diponk24/project-jafar-prosthetic-arm/JAFAR CAD pre-modified/ARM/DIFFERENTIAL/TOP.stl

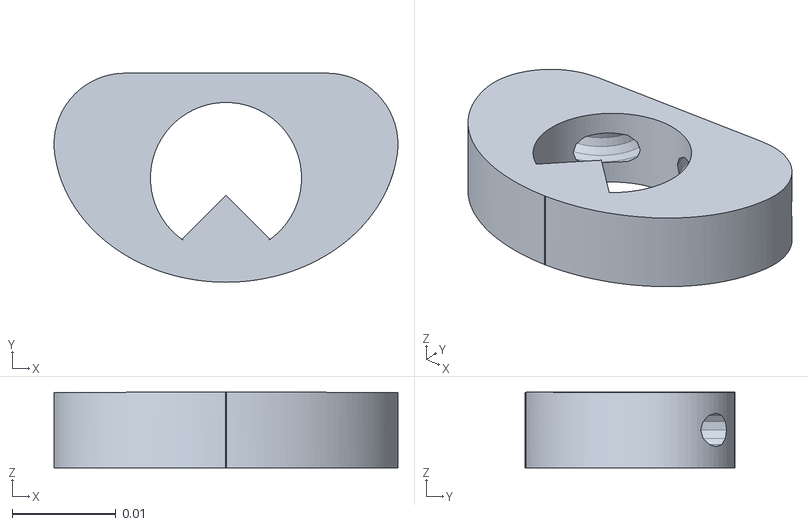
[picture p24: CAD file, 2026-06-13]
JAFAR CAD pre-modified/ARM/DIFFERENTIAL/TOP.stl
0.0332 x 0.0202 x 0.00731
