diponk24/project-jafar-prosthetic-arm/JAFAR CAD post modification/Fingers/Arm/base.stl

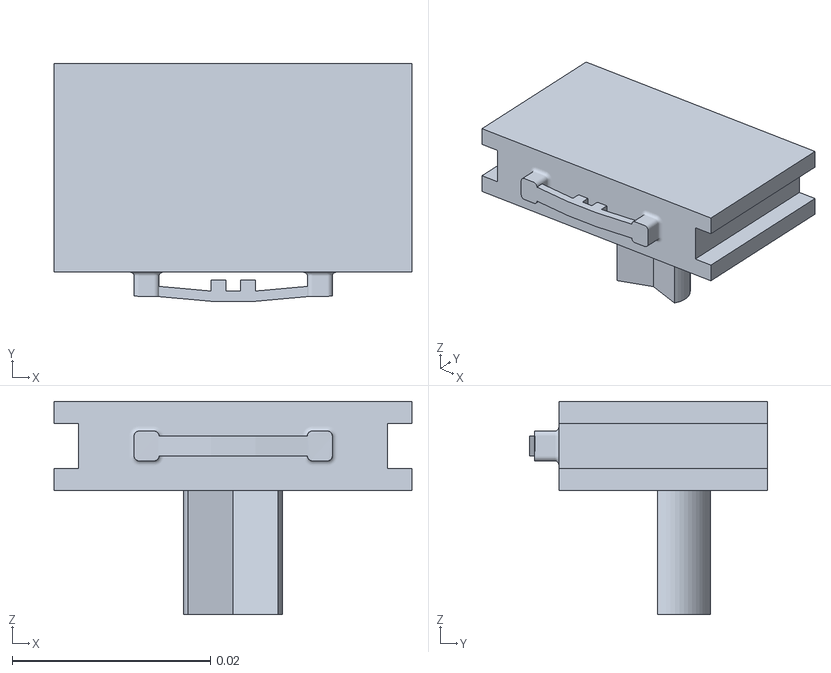
[picture p25: CAD file, 2026-06-13]
JAFAR CAD post modification/Fingers/Arm/base.stl
0.0361 x 0.0239 x 0.0215
