diponk24/project-jafar-prosthetic-arm/JAFAR CAD post modification/Fingers/little_m.stl

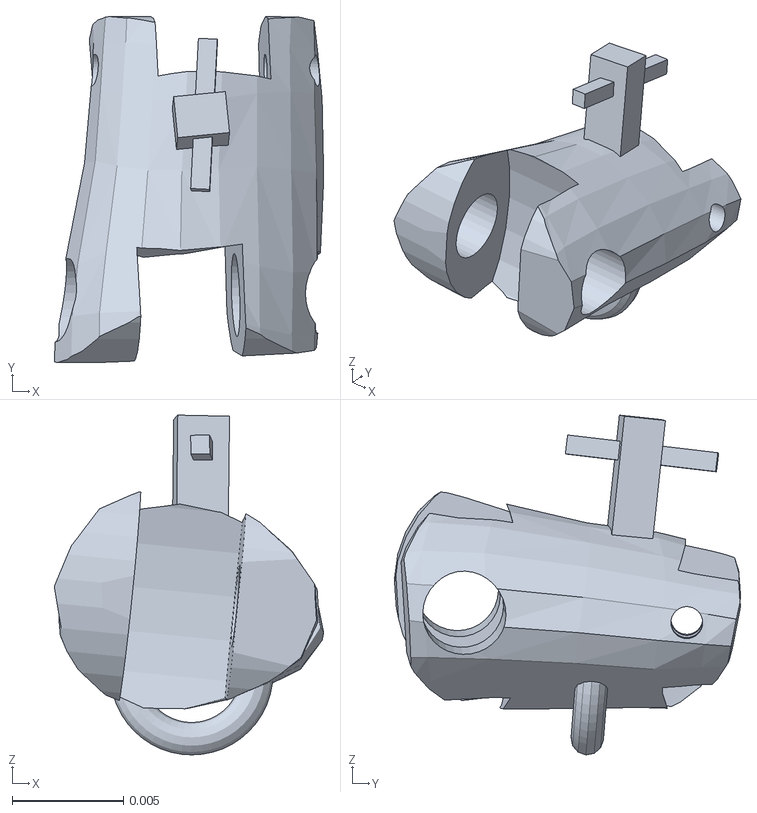
[picture p26: CAD file, 2026-06-13]
JAFAR CAD post modification/Fingers/little_m.stl
0.0121 x 0.0155 x 0.0152
