diponk24/project-jafar-prosthetic-arm/JAFAR CAD pre-modified/ARM/DIFFERENTIAL/PALM/INDEX/1.stl

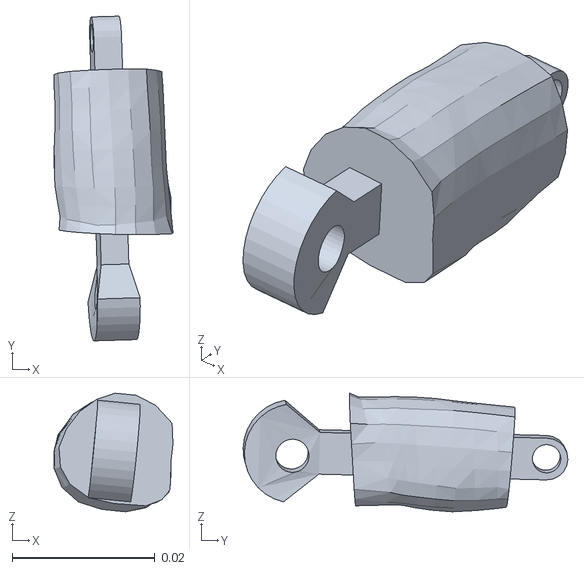
[picture p27: CAD file, 2026-06-13]
JAFAR CAD pre-modified/ARM/DIFFERENTIAL/PALM/INDEX/1.stl
0.0167 x 0.0455 x 0.0166
