diponk24/project-jafar-prosthetic-arm/JAFAR CAD pre-modified/ARM/DIFFERENTIAL/PALM/LITTLE/3.stl

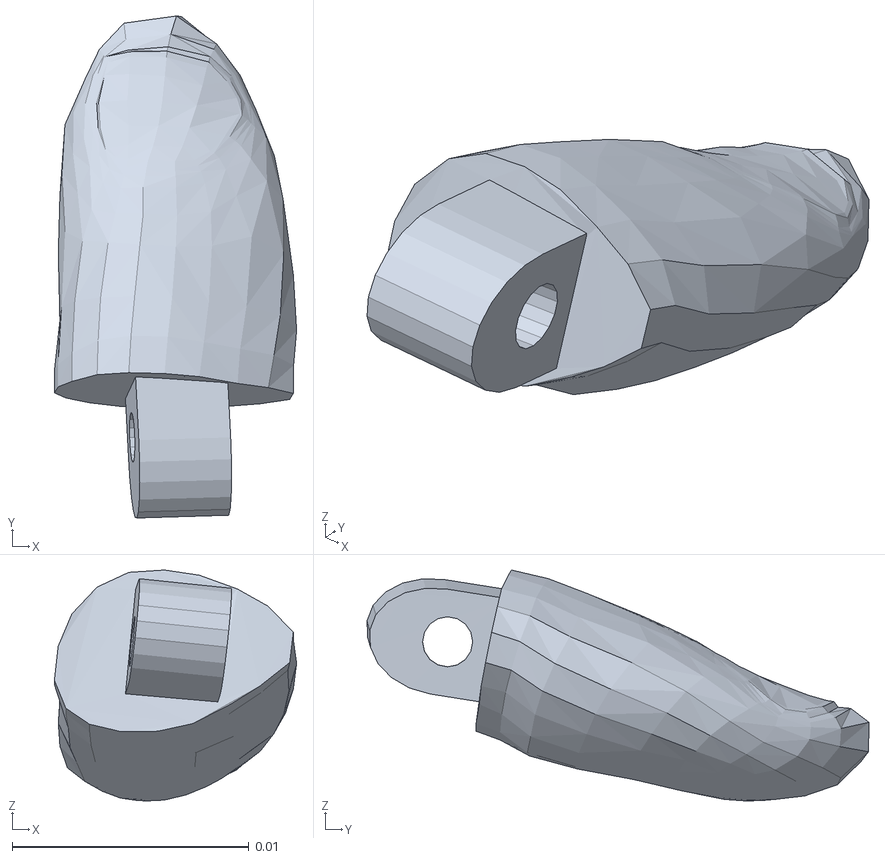
[picture p28: CAD file, 2026-06-13]
JAFAR CAD pre-modified/ARM/DIFFERENTIAL/PALM/LITTLE/3.stl
0.0102 x 0.0212 x 0.00975
