diponk24/project-jafar-prosthetic-arm/JAFAR CAD pre-modified/ARM/DIFFERENTIAL/PALM/MID/2.stl

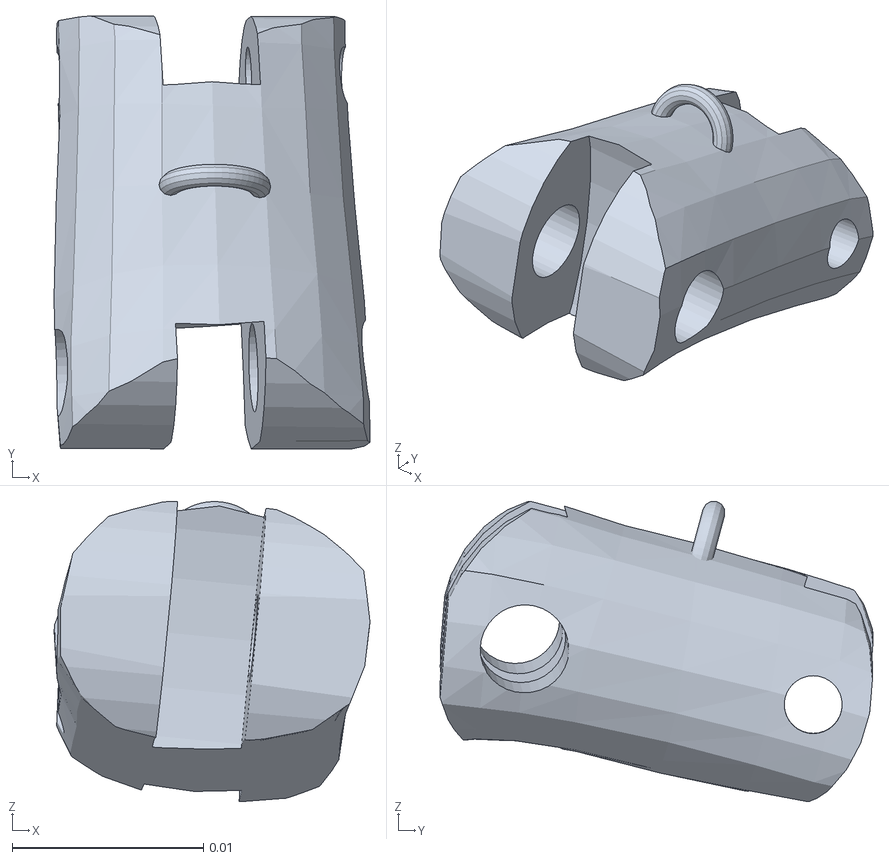
[picture p29: CAD file, 2026-06-13]
JAFAR CAD pre-modified/ARM/DIFFERENTIAL/PALM/MID/2.stl
0.0165 x 0.0226 x 0.0157
