diponk24/project-jafar-prosthetic-arm/JAFAR CAD pre-modified/ARM/DIFFERENTIAL/PALM/RING/1.stl

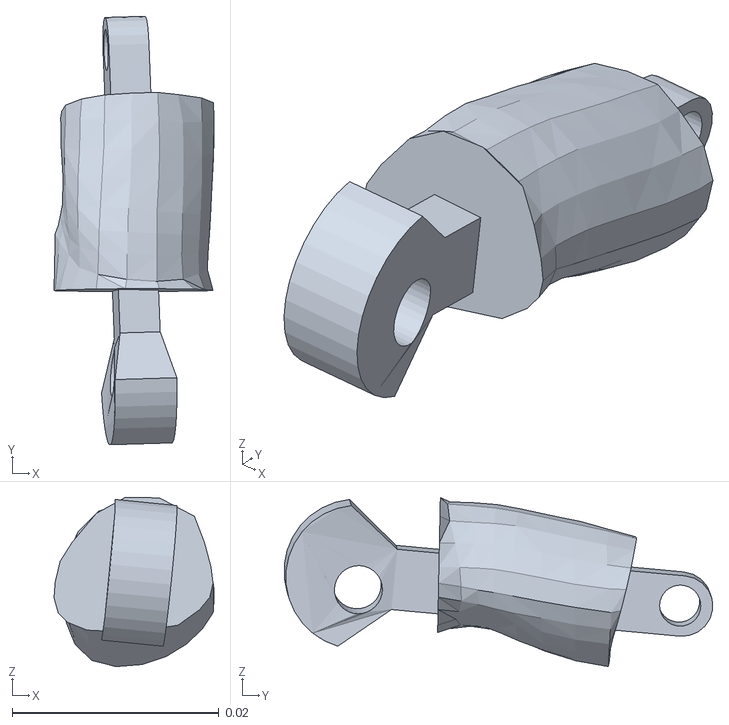
[picture p30: CAD file, 2026-06-13]
JAFAR CAD pre-modified/ARM/DIFFERENTIAL/PALM/RING/1.stl
0.0155 x 0.0414 x 0.0163
