diponk24/project-jafar-prosthetic-arm/JAFAR CAD post modification/Fingers/Arm/cylinder.stl

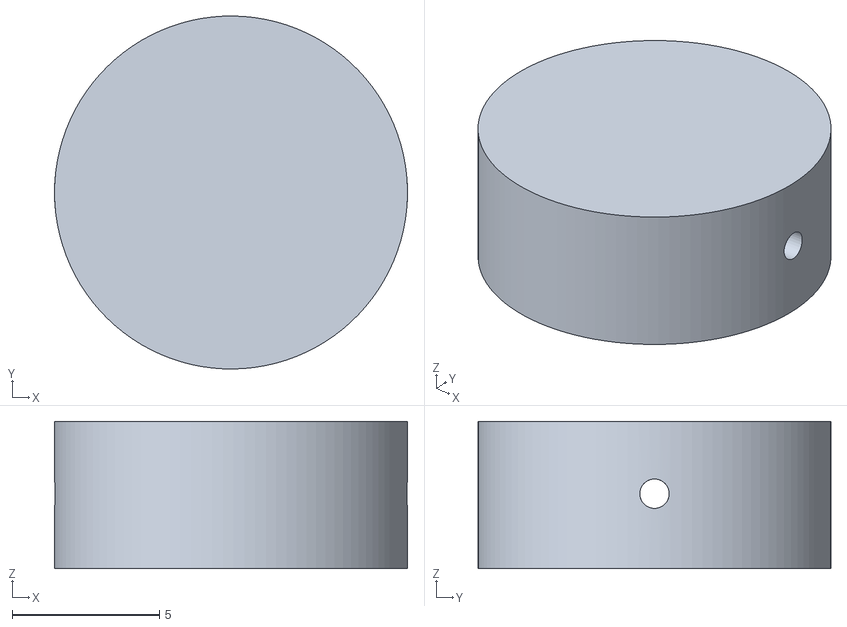
[picture p31: CAD file, 2026-06-13]
JAFAR CAD post modification/Fingers/Arm/cylinder.stl
12.0 x 12.0 x 5.00
