diponk24/project-jafar-prosthetic-arm/JAFAR CAD post modification/Fingers/m_d.stl

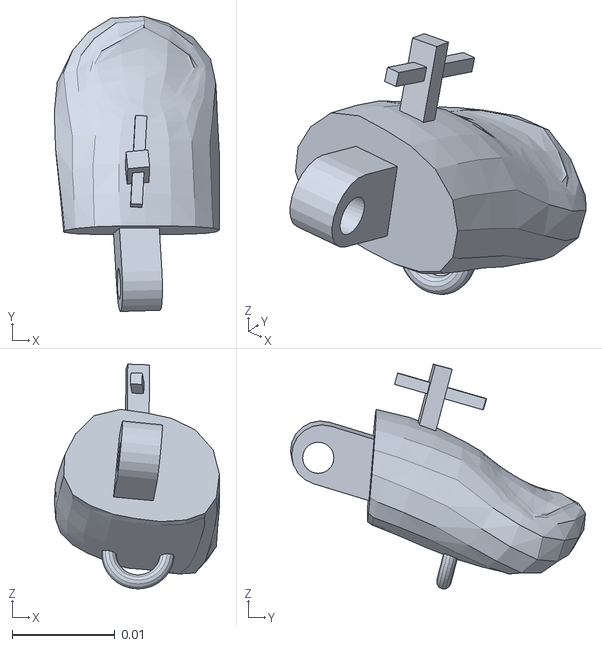
[picture p32: CAD file, 2026-06-13]
JAFAR CAD post modification/Fingers/m_d.stl
0.0161 x 0.0287 x 0.0219
