diponk24/project-jafar-prosthetic-arm/JAFAR CAD post modification/Fingers/index lowee.stl

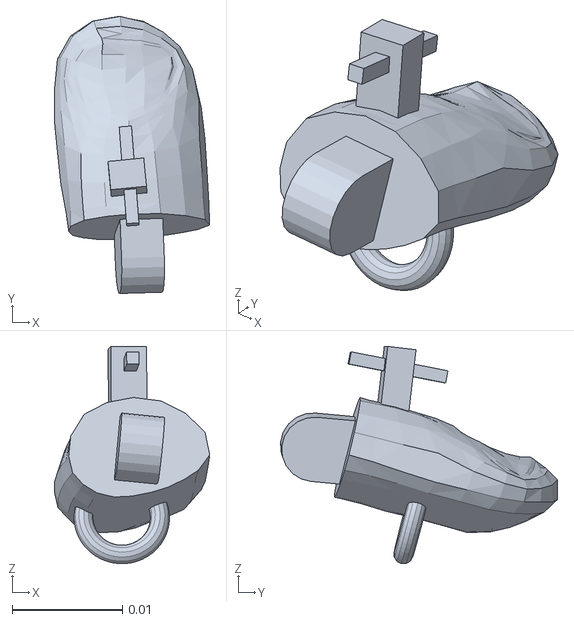
[picture p33: CAD file, 2026-06-13]
JAFAR CAD post modification/Fingers/index lowee.stl
0.0141 x 0.0251 x 0.0197
