diponk24/project-jafar-prosthetic-arm/JAFAR CAD post modification/Fingers/m_d stl.stl

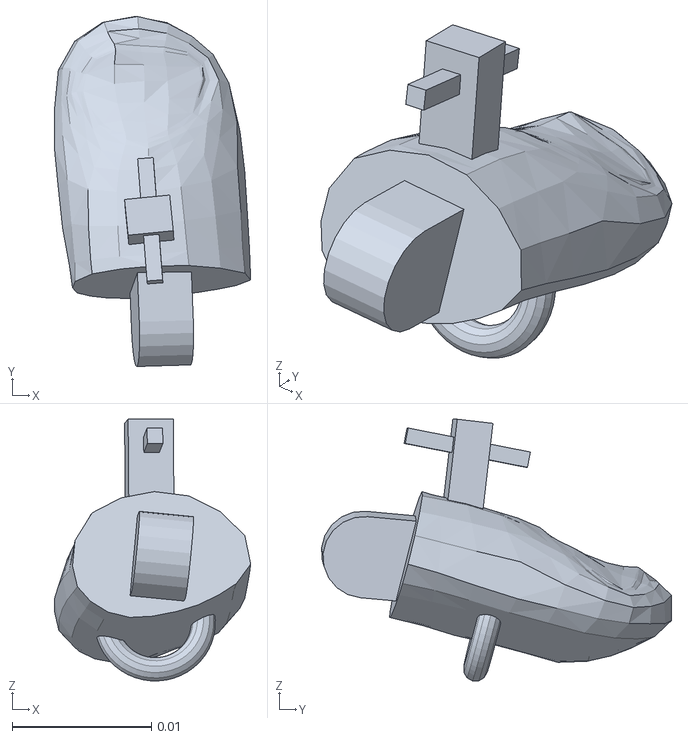
[picture p35: CAD file, 2026-06-13]
JAFAR CAD post modification/Fingers/m_d stl.stl
0.0141 x 0.0251 x 0.0188
