diponk24/project-jafar-prosthetic-arm/JAFAR CAD post modification/Fingers/mid upper.stl

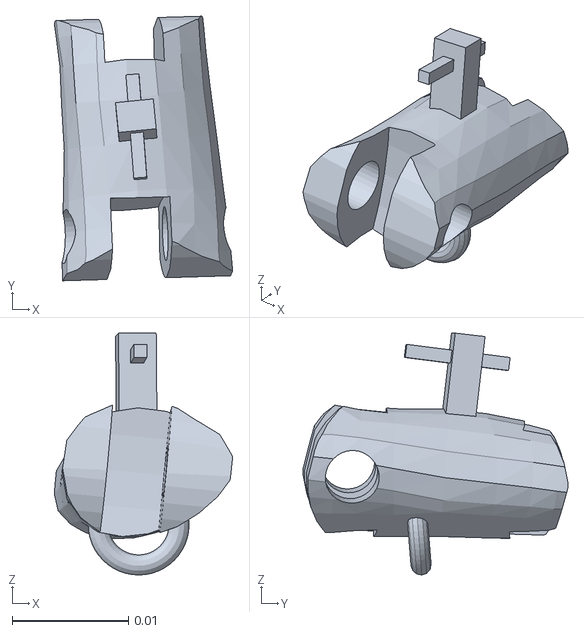
[picture p36: CAD file, 2026-06-13]
JAFAR CAD post modification/Fingers/mid upper.stl
0.0153 x 0.0227 x 0.0208
