diponk24/project-jafar-prosthetic-arm/JAFAR CAD post modification/Fingers/r_d stl.stl

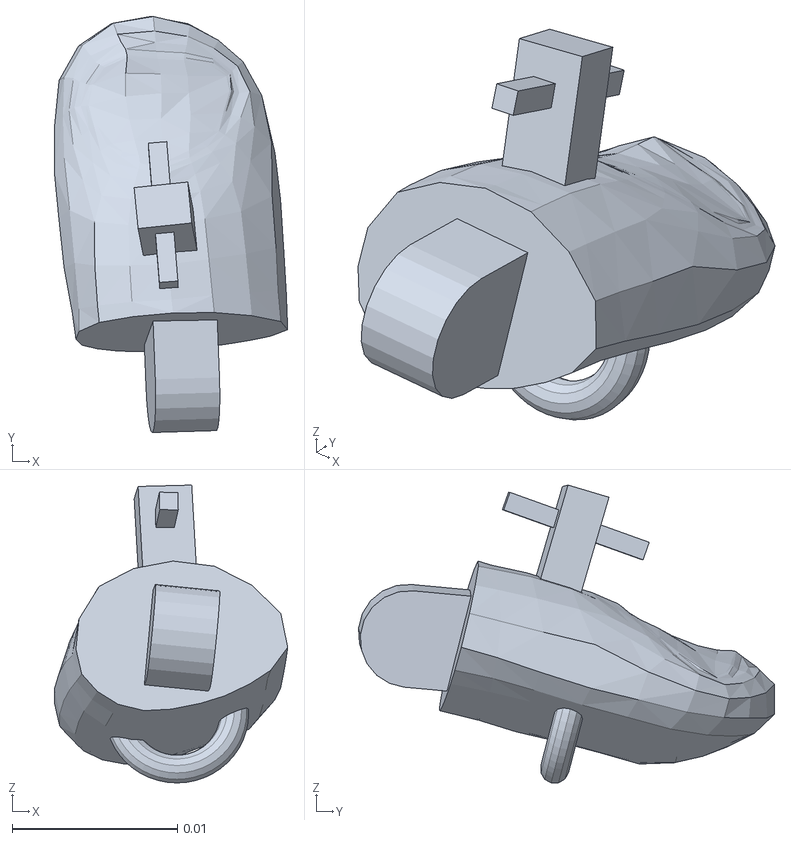
[picture p37: CAD file, 2026-06-13]
JAFAR CAD post modification/Fingers/r_d stl.stl
0.0141 x 0.0251 x 0.018
