diponk24/project-jafar-prosthetic-arm/JAFAR CAD post modification/Fingers/little_d.stl

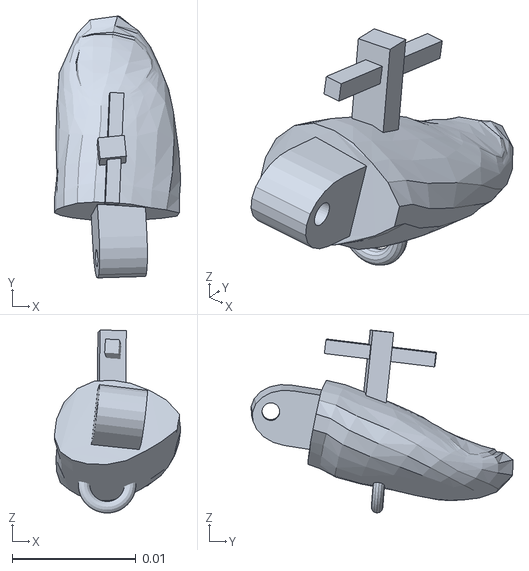
[picture p39: CAD file, 2026-06-13]
JAFAR CAD post modification/Fingers/little_d.stl
0.0102 x 0.0212 x 0.0148
