diponk24/project-jafar-prosthetic-arm/JAFAR CAD post modification/Fingers/l_d stl.stl

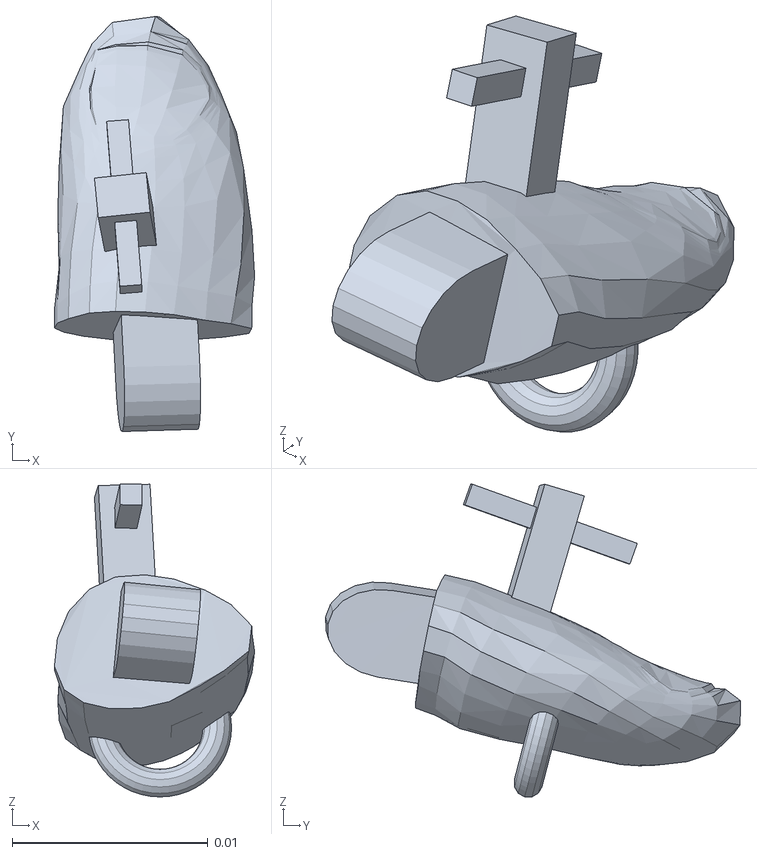
[picture p40: CAD file, 2026-06-13]
JAFAR CAD post modification/Fingers/l_d stl.stl
0.0102 x 0.0212 x 0.016
